tjussu/open_g/software/firmware_display_board/main/UART.h

#ifndef UART_H
#define UART_H

#include "freertos/FreeRTOS.h"
#include "freertos/task.h"
#include "freertos/queue.h"

extern QueueHandle_t load_queue;
extern QueueHandle_t alarm_queue;
extern QueueHandle_t button_queue;

void uart_event_task(void * args);



#endif
